googlecreativelab/anypixel/frontend/examples/ballpit/README.md

# Anypixel Ball-pit

A 2d ball pit mural for Anypixel. Press and hold an anypixel button to create a ball and grow it larger and larger; drag across buttons to create many, or mash buttons simultaneously to grow them and pit them against each other. Create balls and use them to destroy the hanging Google logo.

**Code:** Kyle Phillips

## Install:

```
npm install
```

## Build:

```
npm run build
```

## Develop:

```
npm run watch
```
