googlecreativelab/anypixel/frontend/examples/squishy/README.md

# anypixel-app-squishy

Built using Box2d and Liquidfun. This project uses a liquid simulation to create gelatinous 'squishy' letters that can be thrown around the board. 

```bash
$ npm install
$ npm run start
```

or to use watch

```bash
$ npm run watch
```
