googlecreativelab/anypixel/frontend/examples/subway/README.md

# Anypixel-Subway

MTA Subway map inspired design. Press a button to reroute the train. Built with the Anypixel Framework. 

To build it:
```sh
npm install
```
or 
```sh
npm run build
```

To run it, you'll need to install [Anypixel-Previewer](https://github.com/googlecreativelab/anypixel-previewer) first. Then in the app's root directory, do:
```sh   
preview
```
