googlecreativelab/anypixel/frontend/examples/blocksquish/preview.jpg

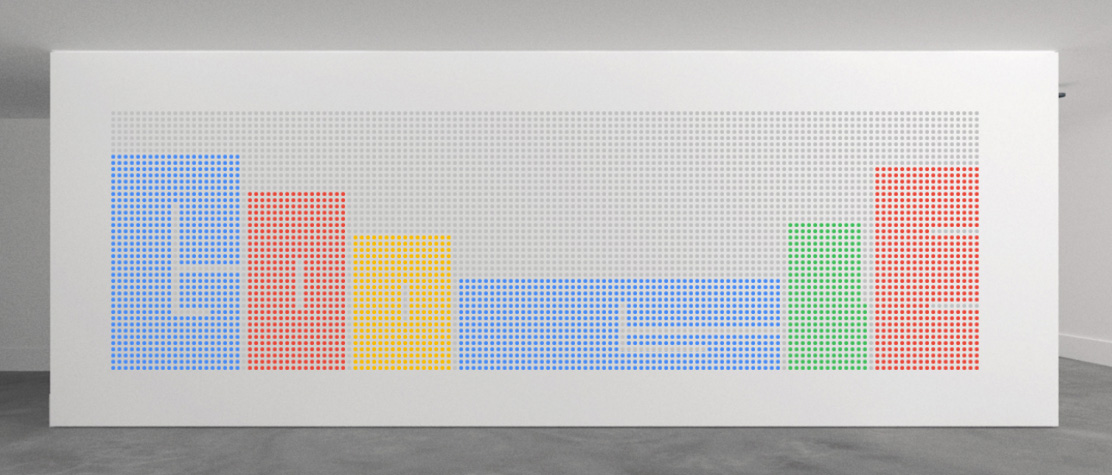
frontend/examples/blocksquish/preview.jpg
