googlecreativelab/anypixel/frontend/examples/heatmap/preview.jpg

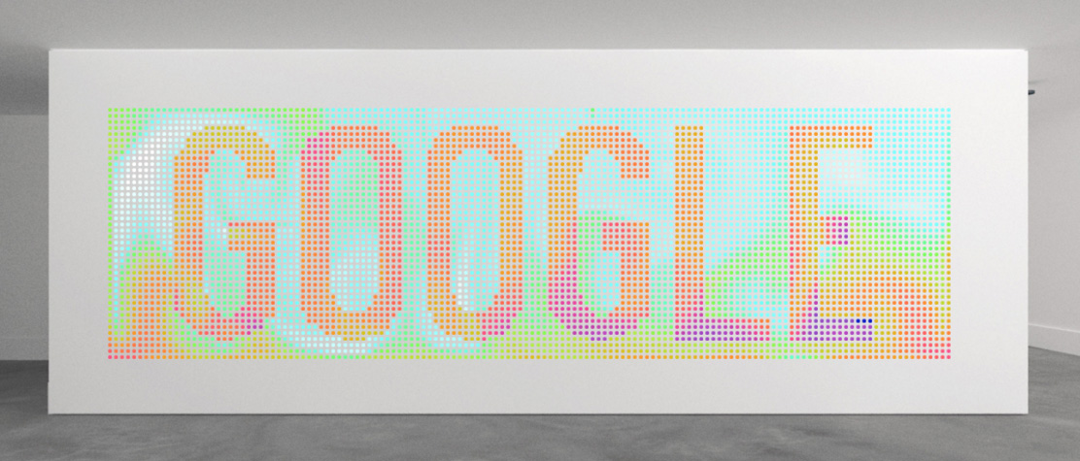
frontend/examples/heatmap/preview.jpg
