googlecreativelab/anypixel/frontend/examples/hyperspace/preview.jpg

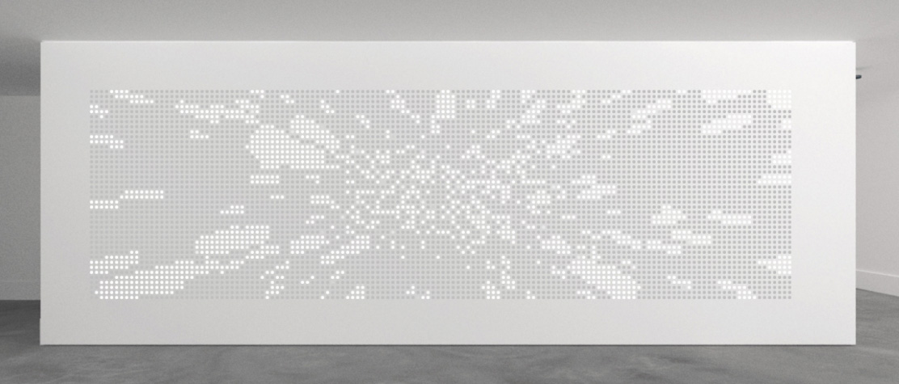
frontend/examples/hyperspace/preview.jpg
