googlecreativelab/anypixel/frontend/examples/reaction/preview.jpg

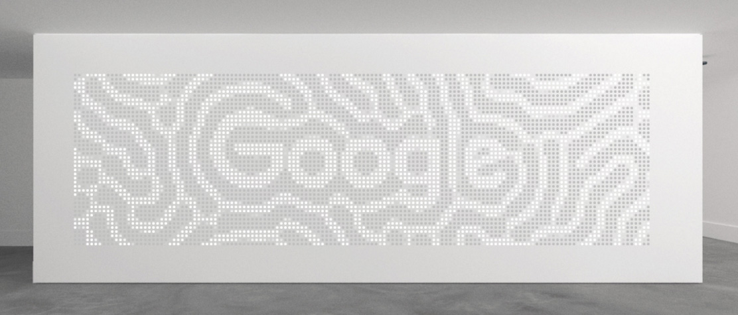
frontend/examples/reaction/preview.jpg
