googlecreativelab/anypixel/hardware/pcb/controller/controller-r3-bottom.pdf

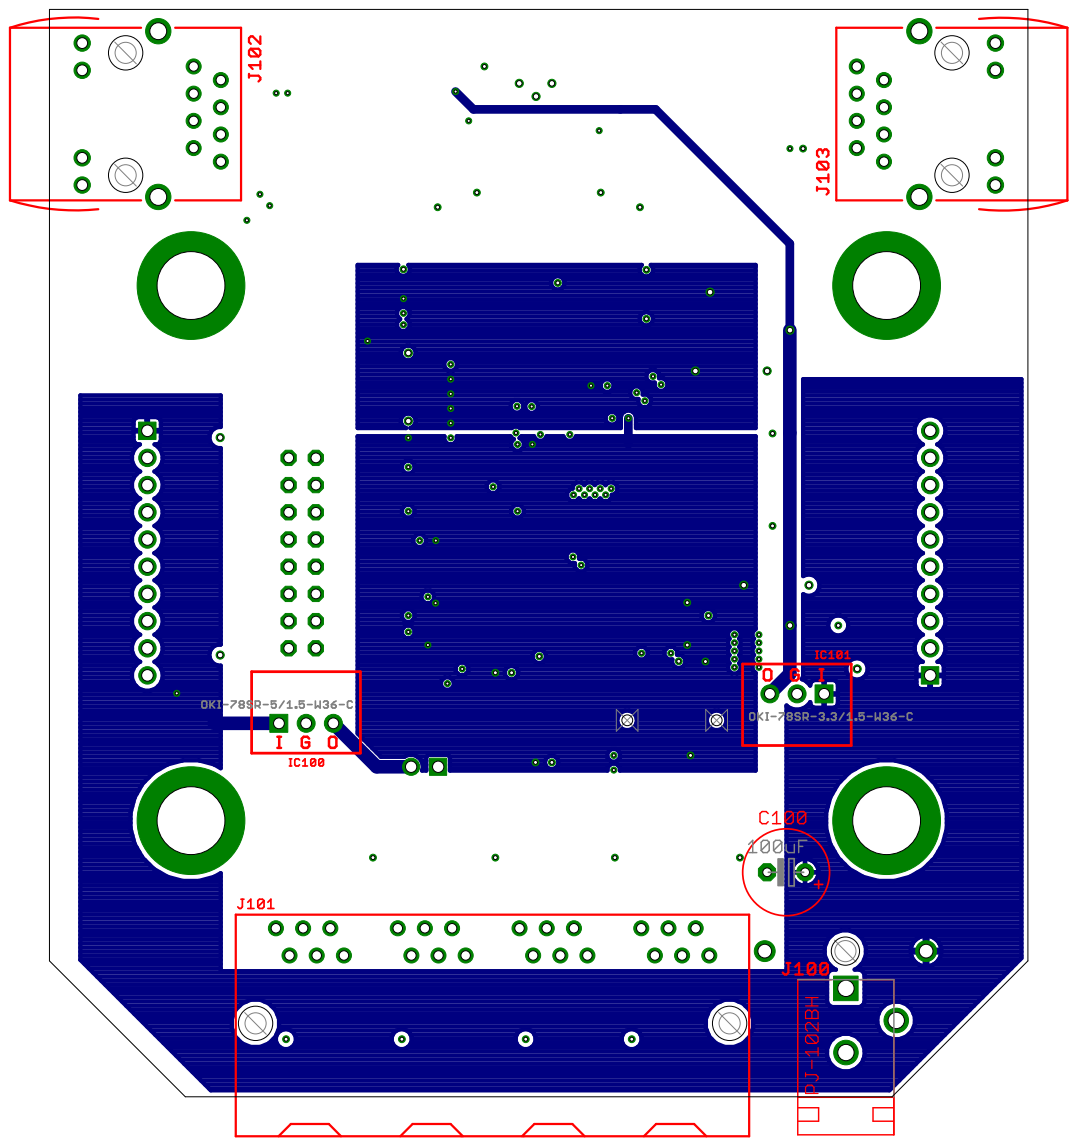
[picture p40: page 1]
