googlecreativelab/anypixel/hardware/pcb/controller/controller-r3-schematics.pdf

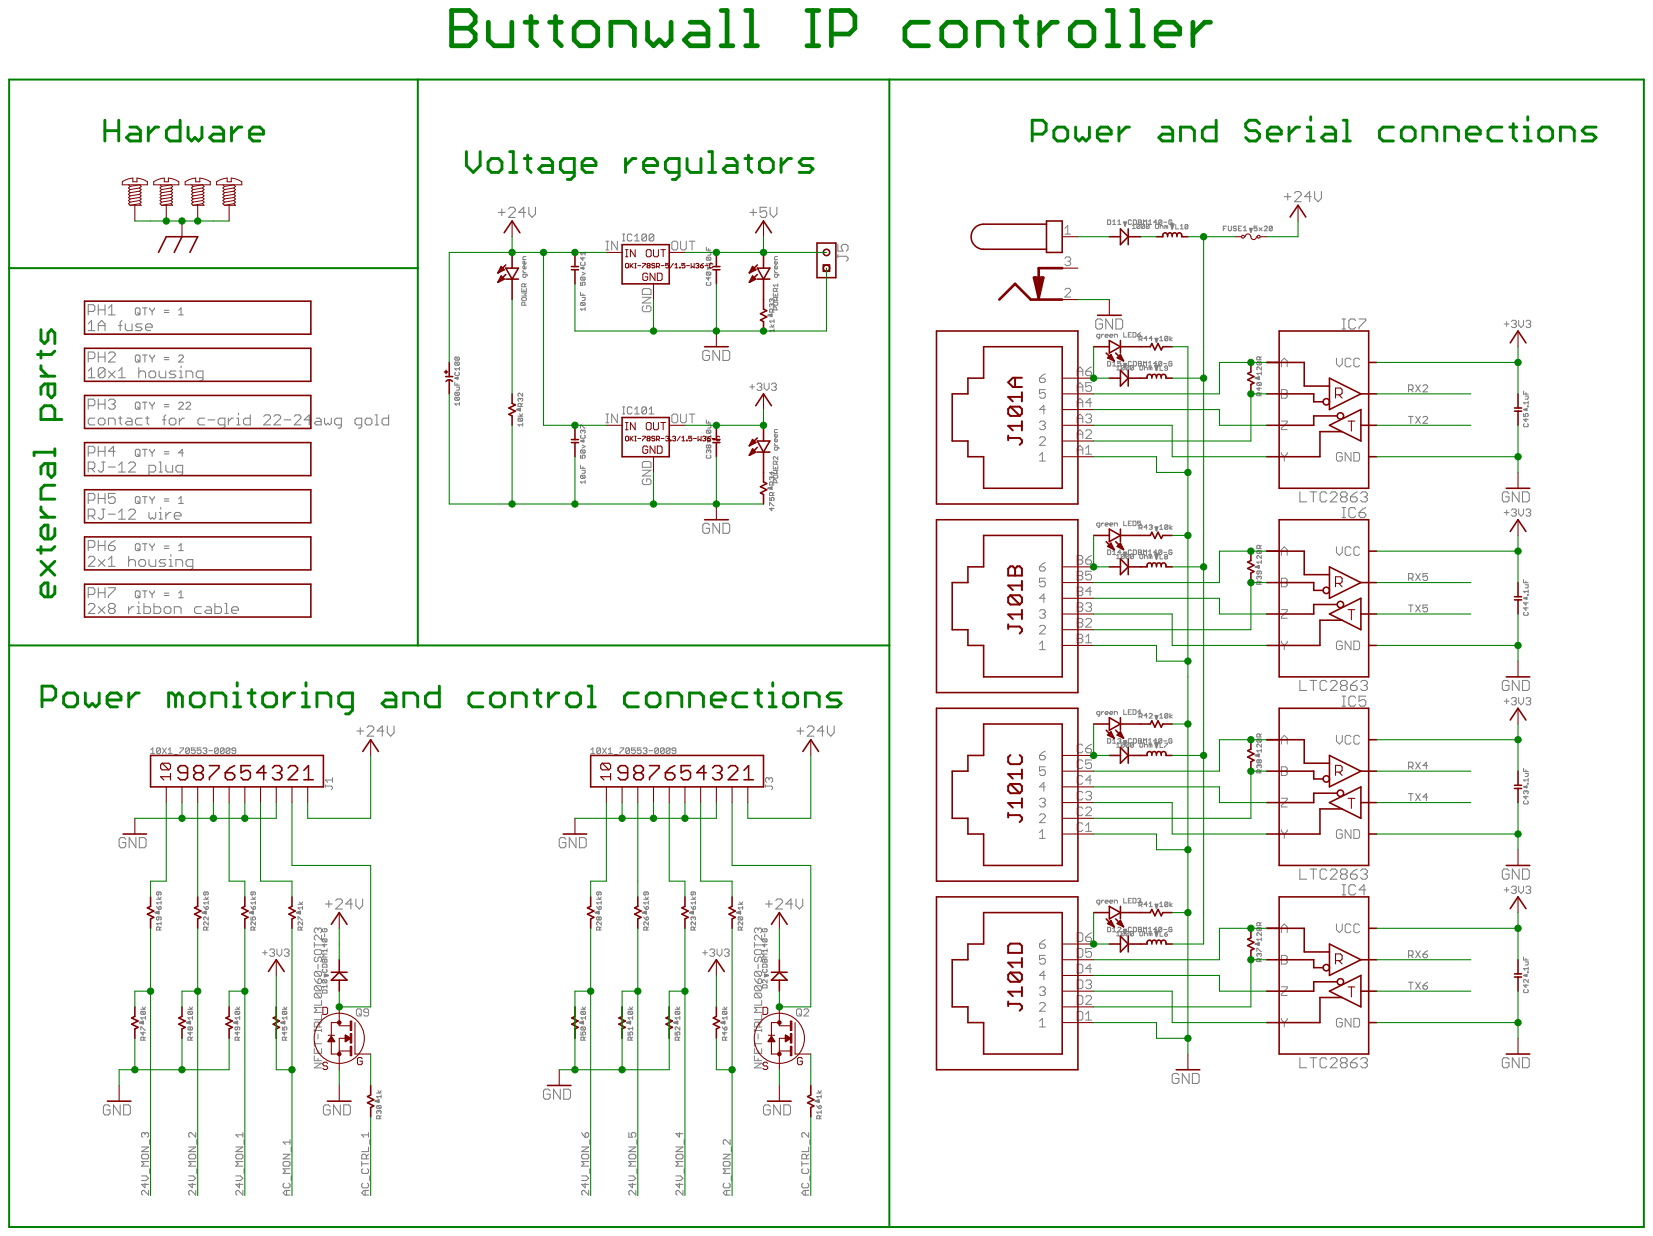
[picture p41: page 1]

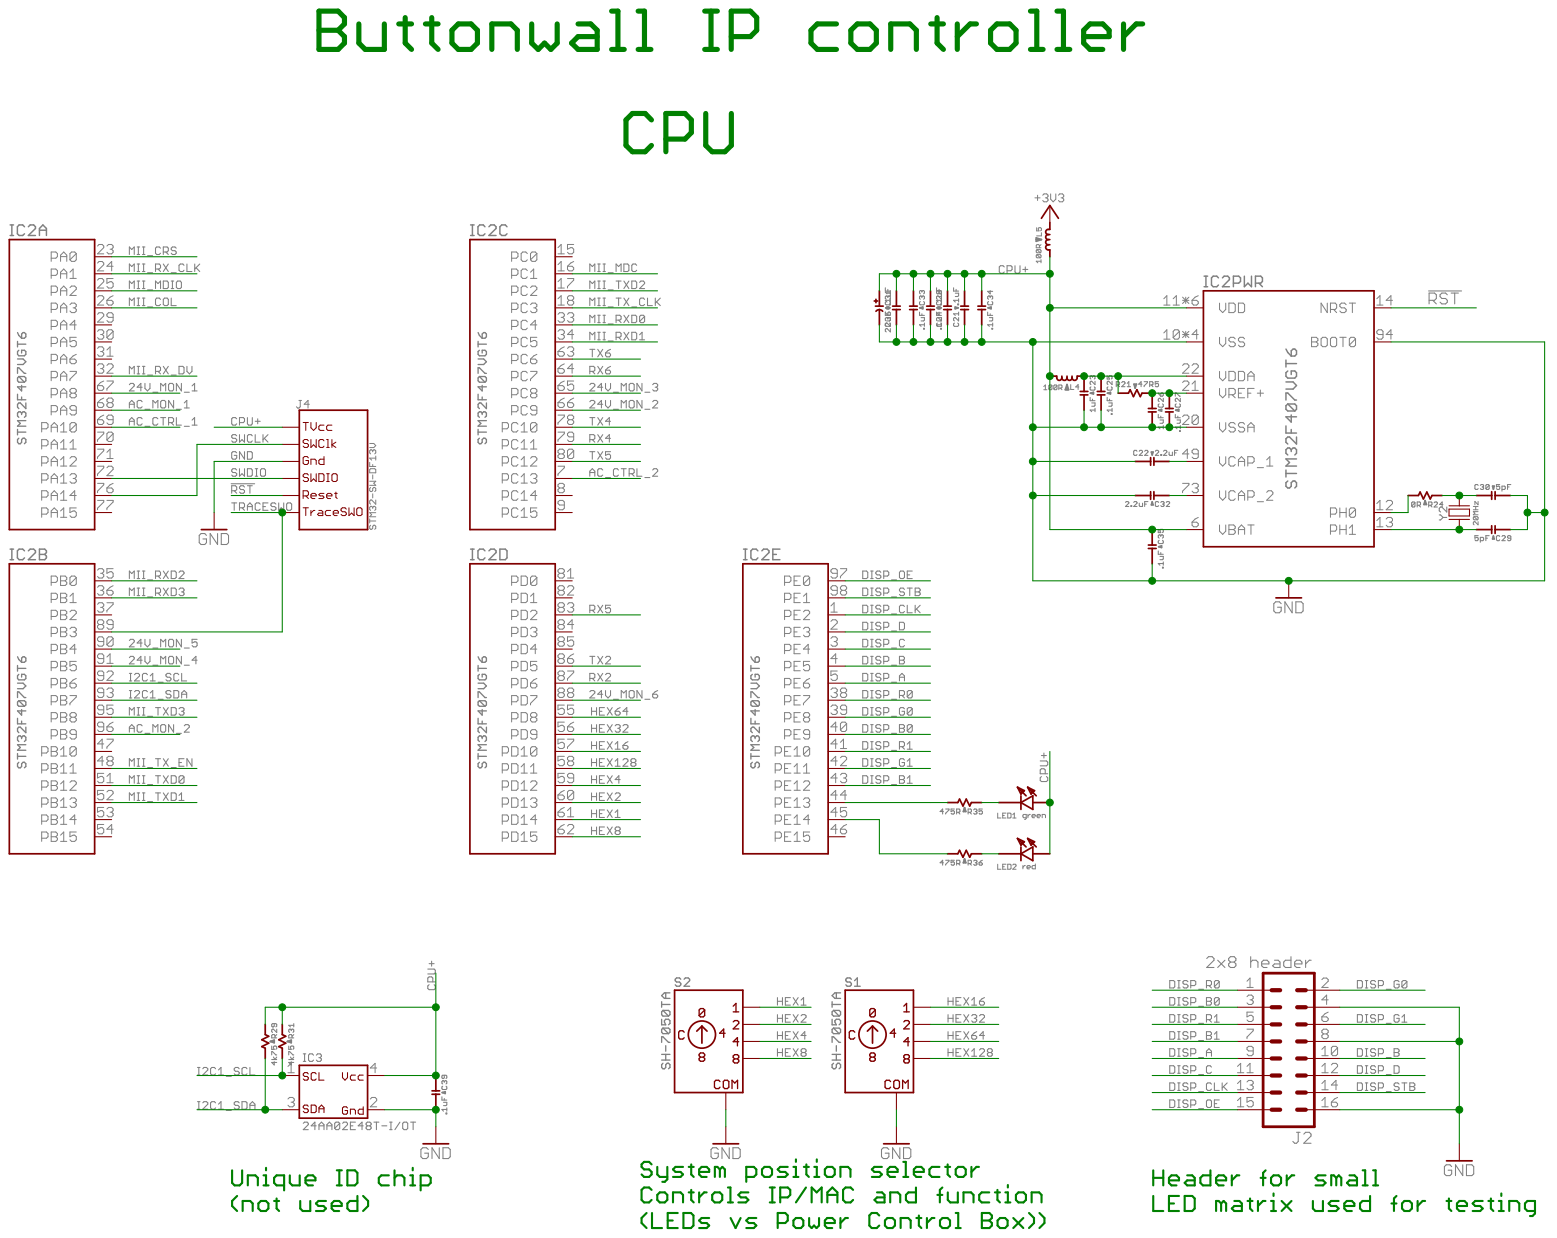
[picture p42: page 2]

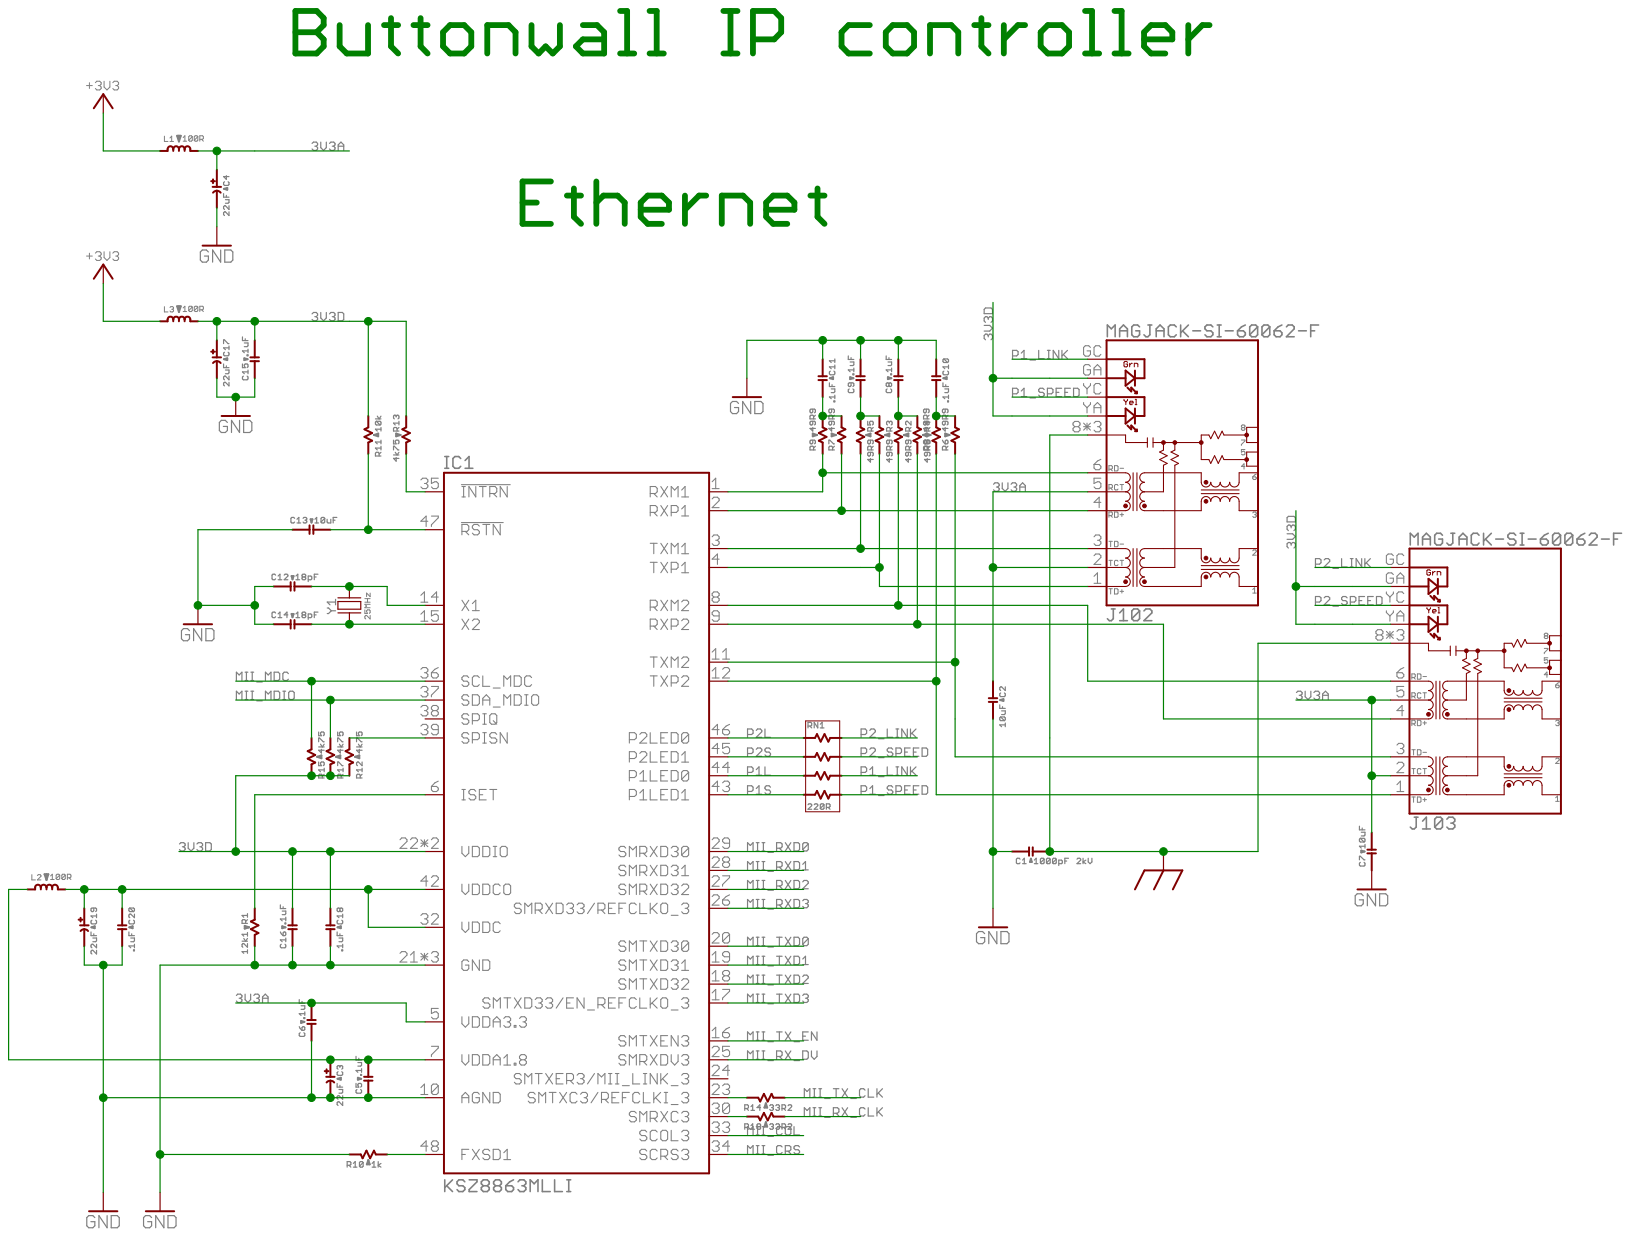
[picture p43: page 3]
