googlecreativelab/anypixel/hardware/pcb/controller/controller-r3-top.pdf

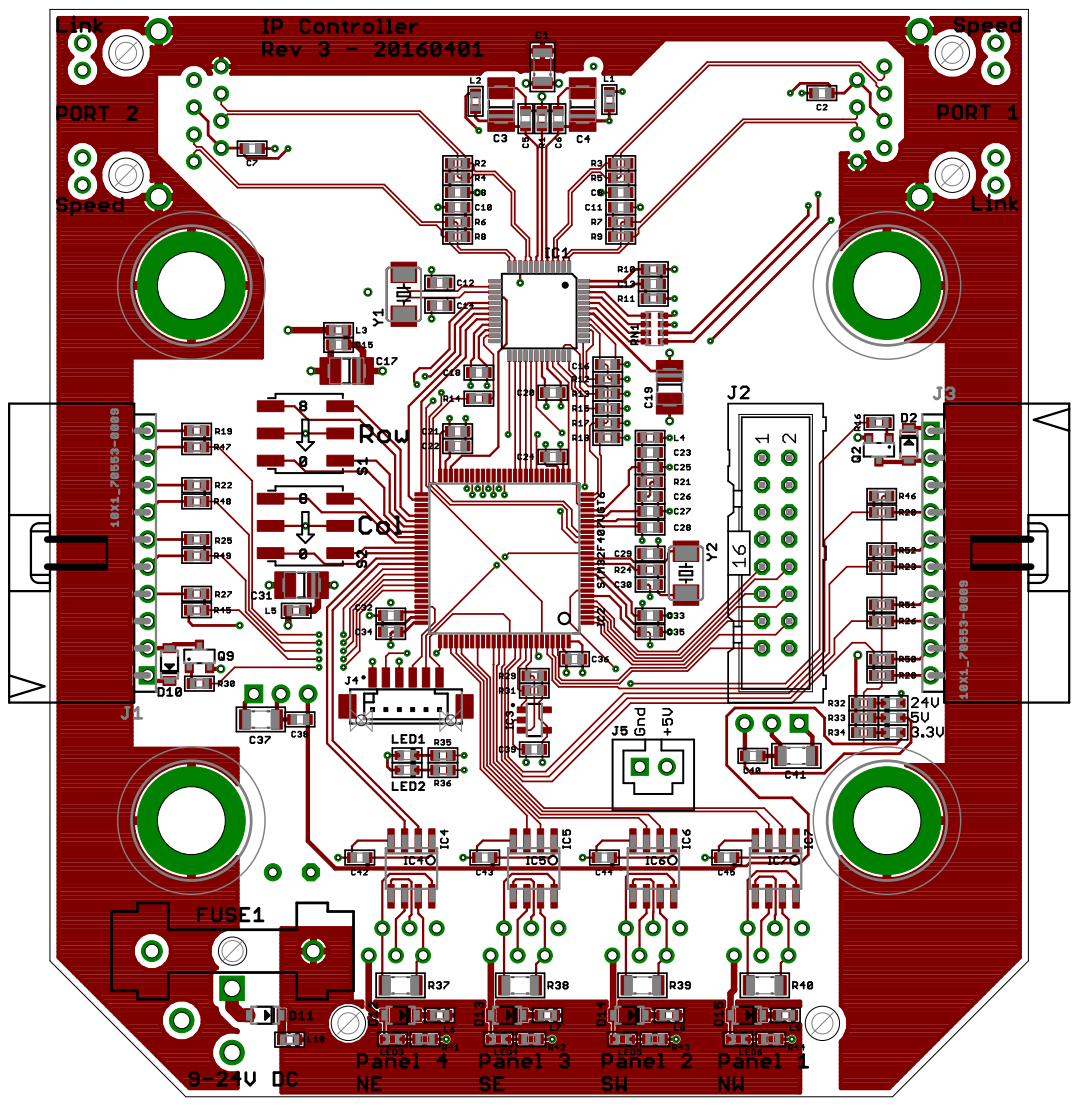
[picture p44: page 1]
