googlecreativelab/anypixel/hardware/pcb/controller/controller-r3.pdf

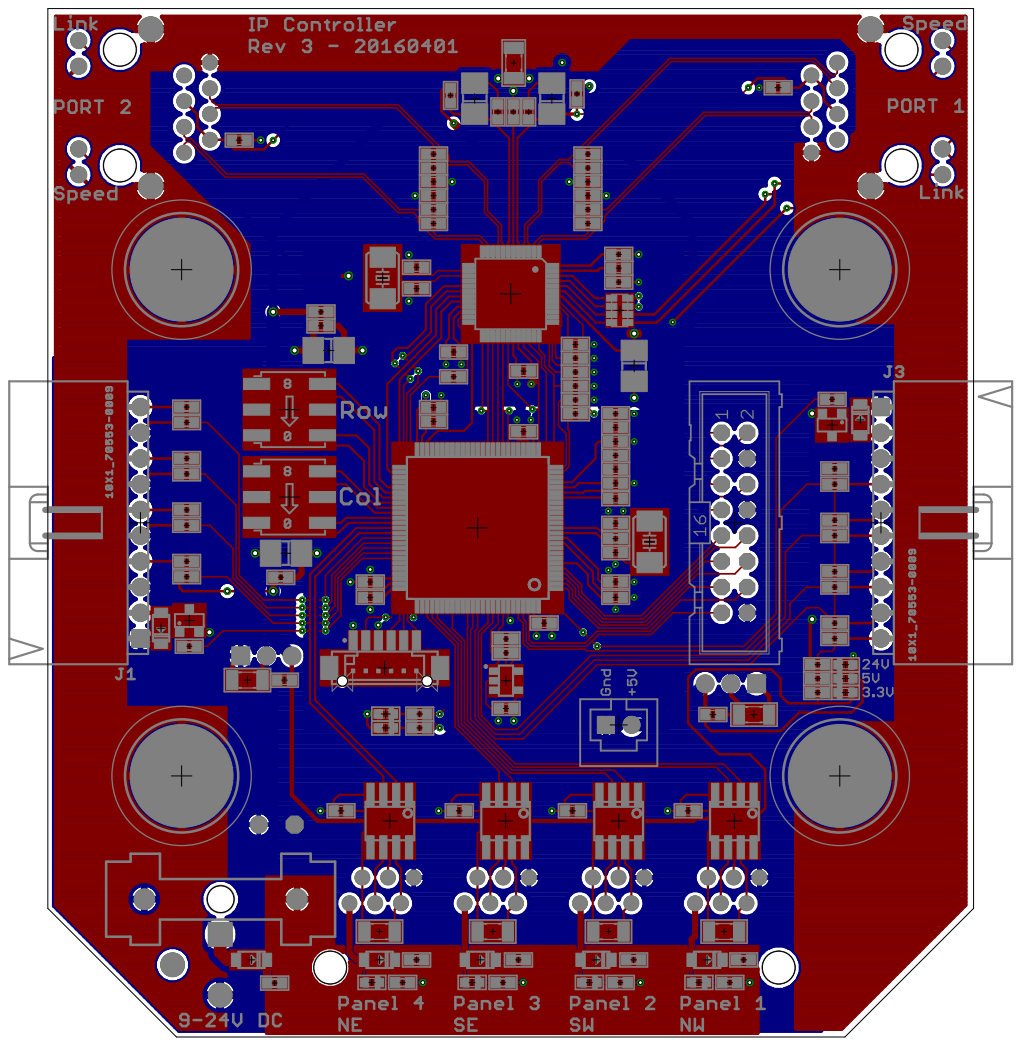
[picture p45: page 1]
