googlecreativelab/anypixel/hardware/pcb/display/display-r2-bottom.pdf

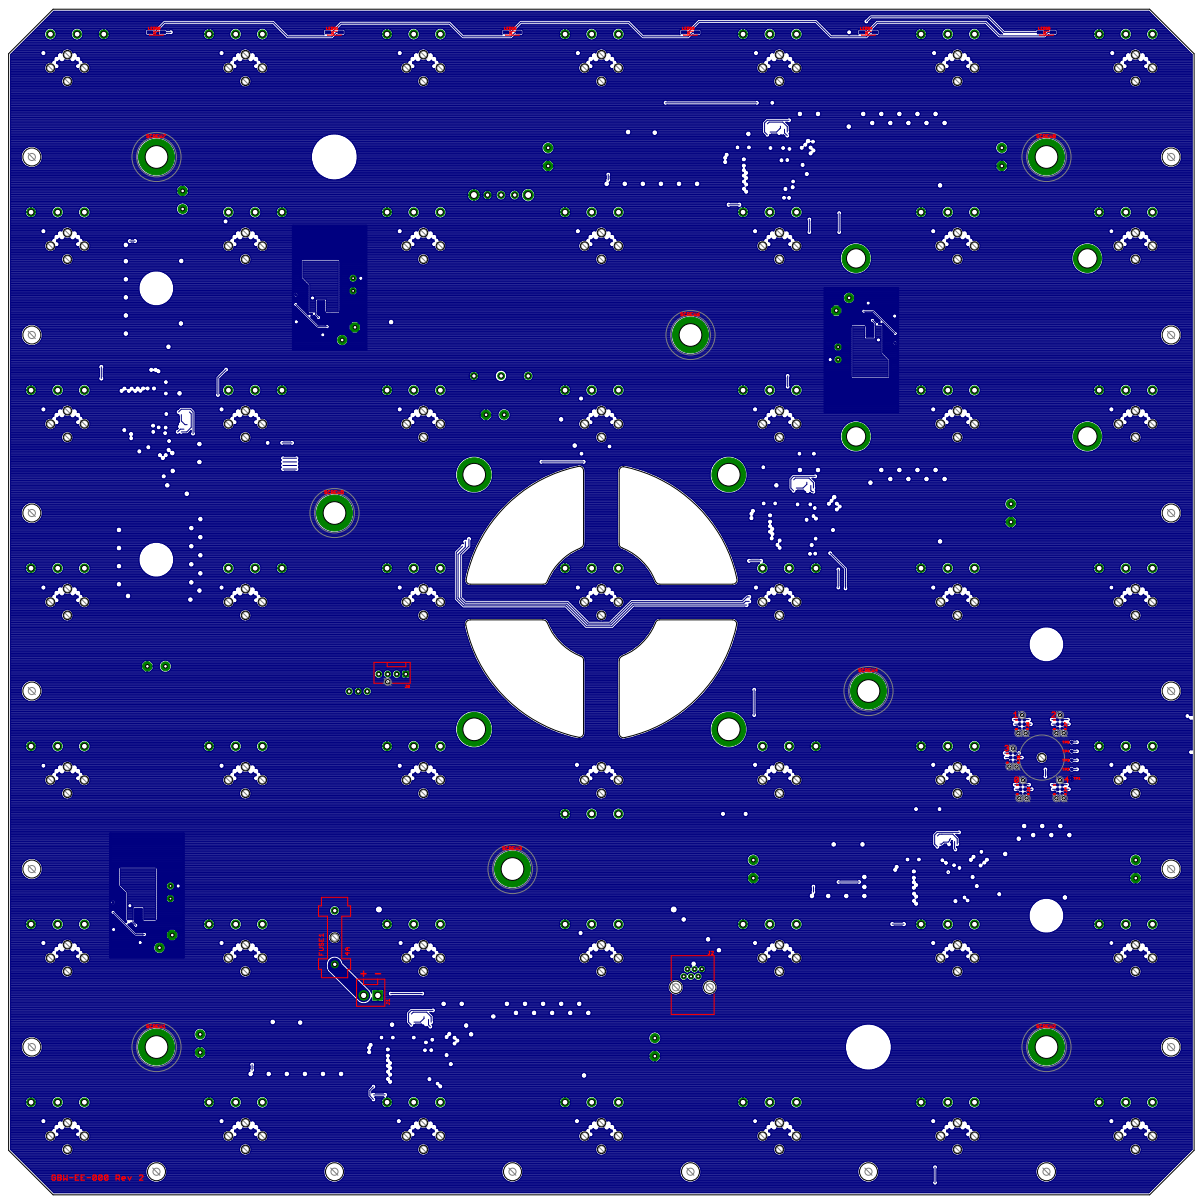
[picture p46: page 1]
