googlecreativelab/anypixel/hardware/pcb/display/display-r2-schematic.pdf

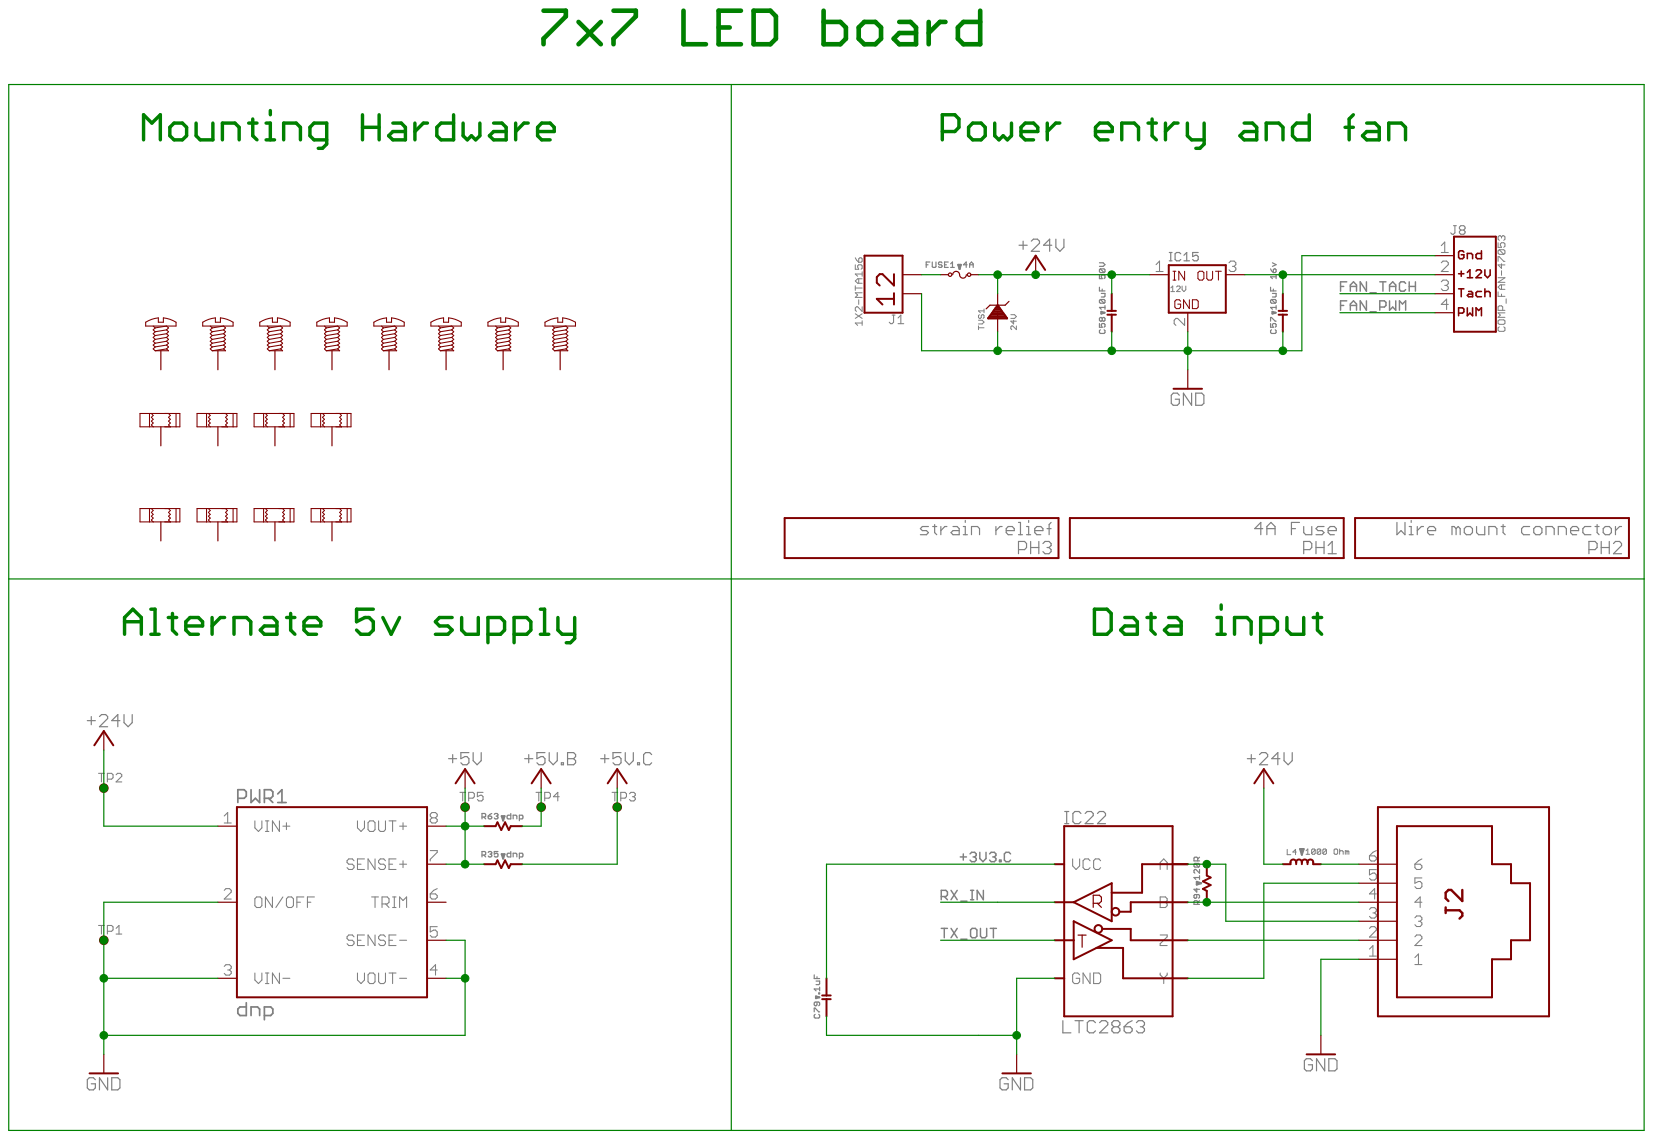
[picture p47: page 1]

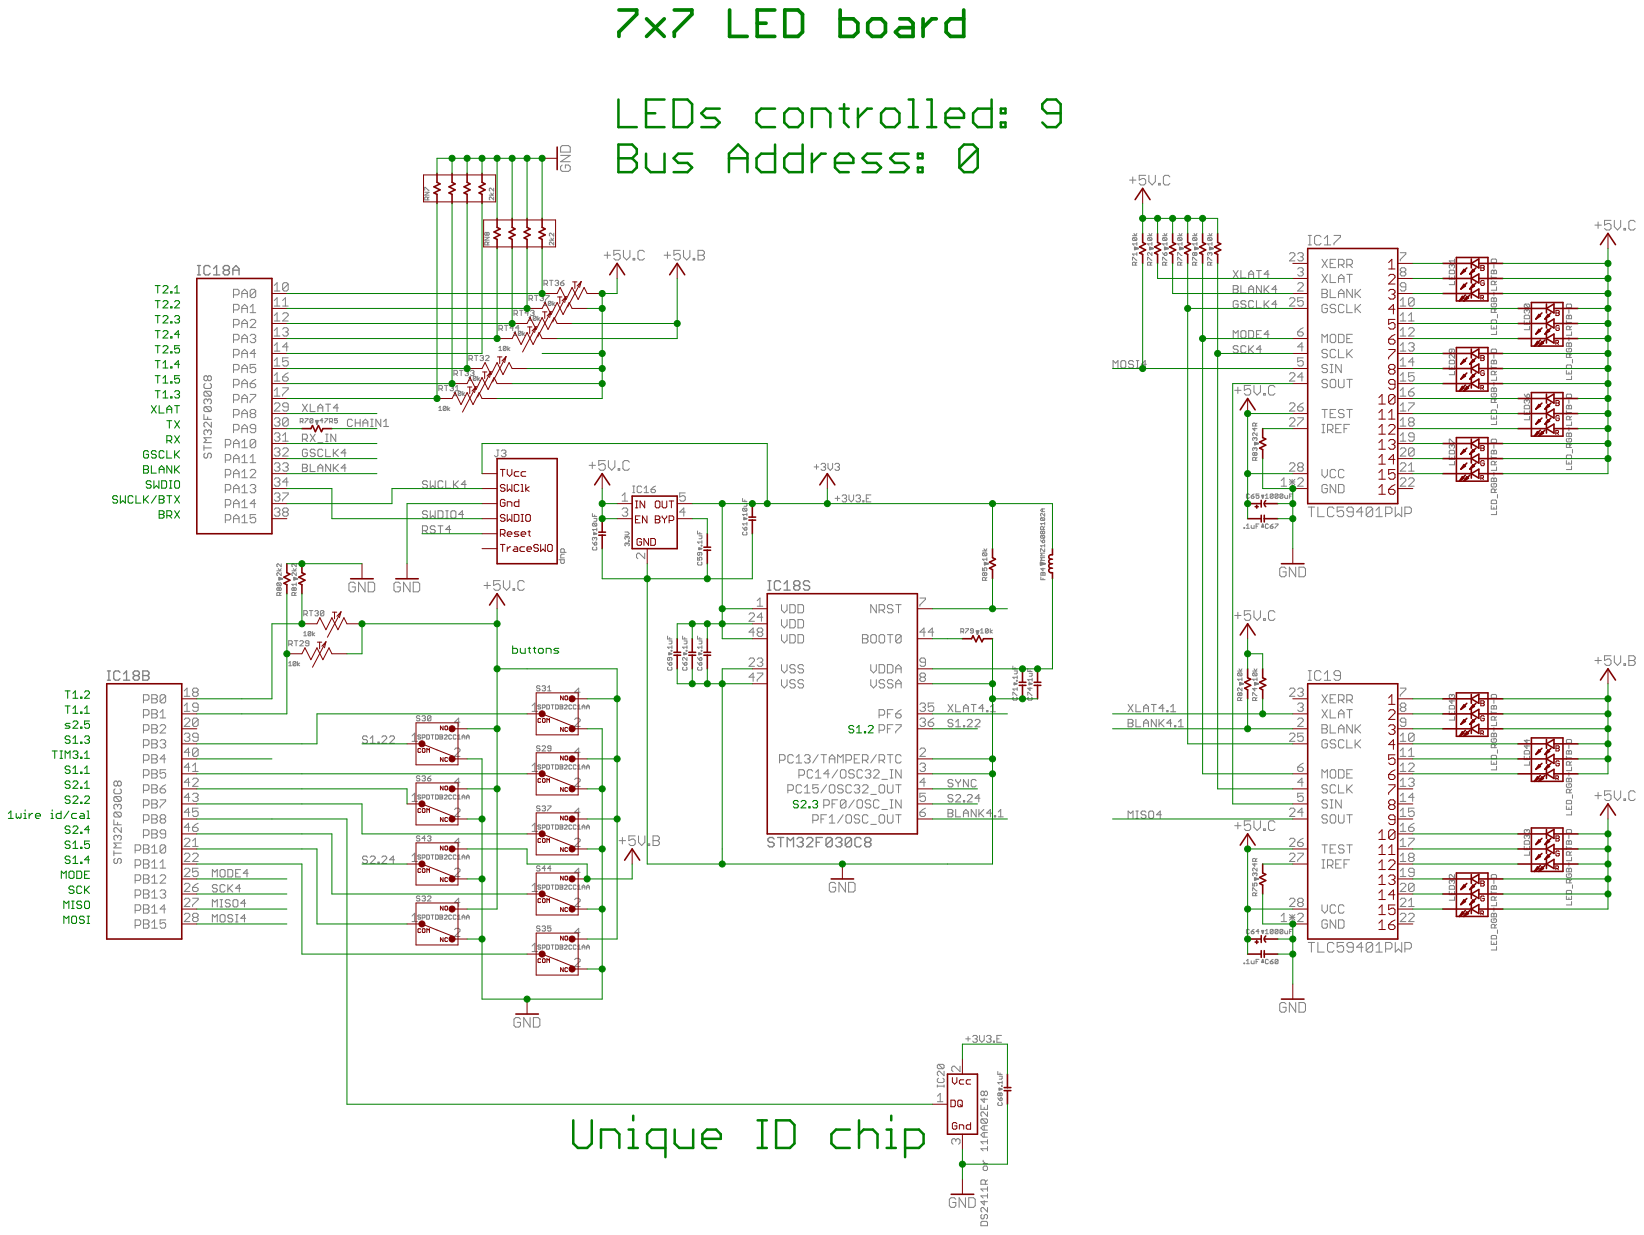
[picture p48: page 2]

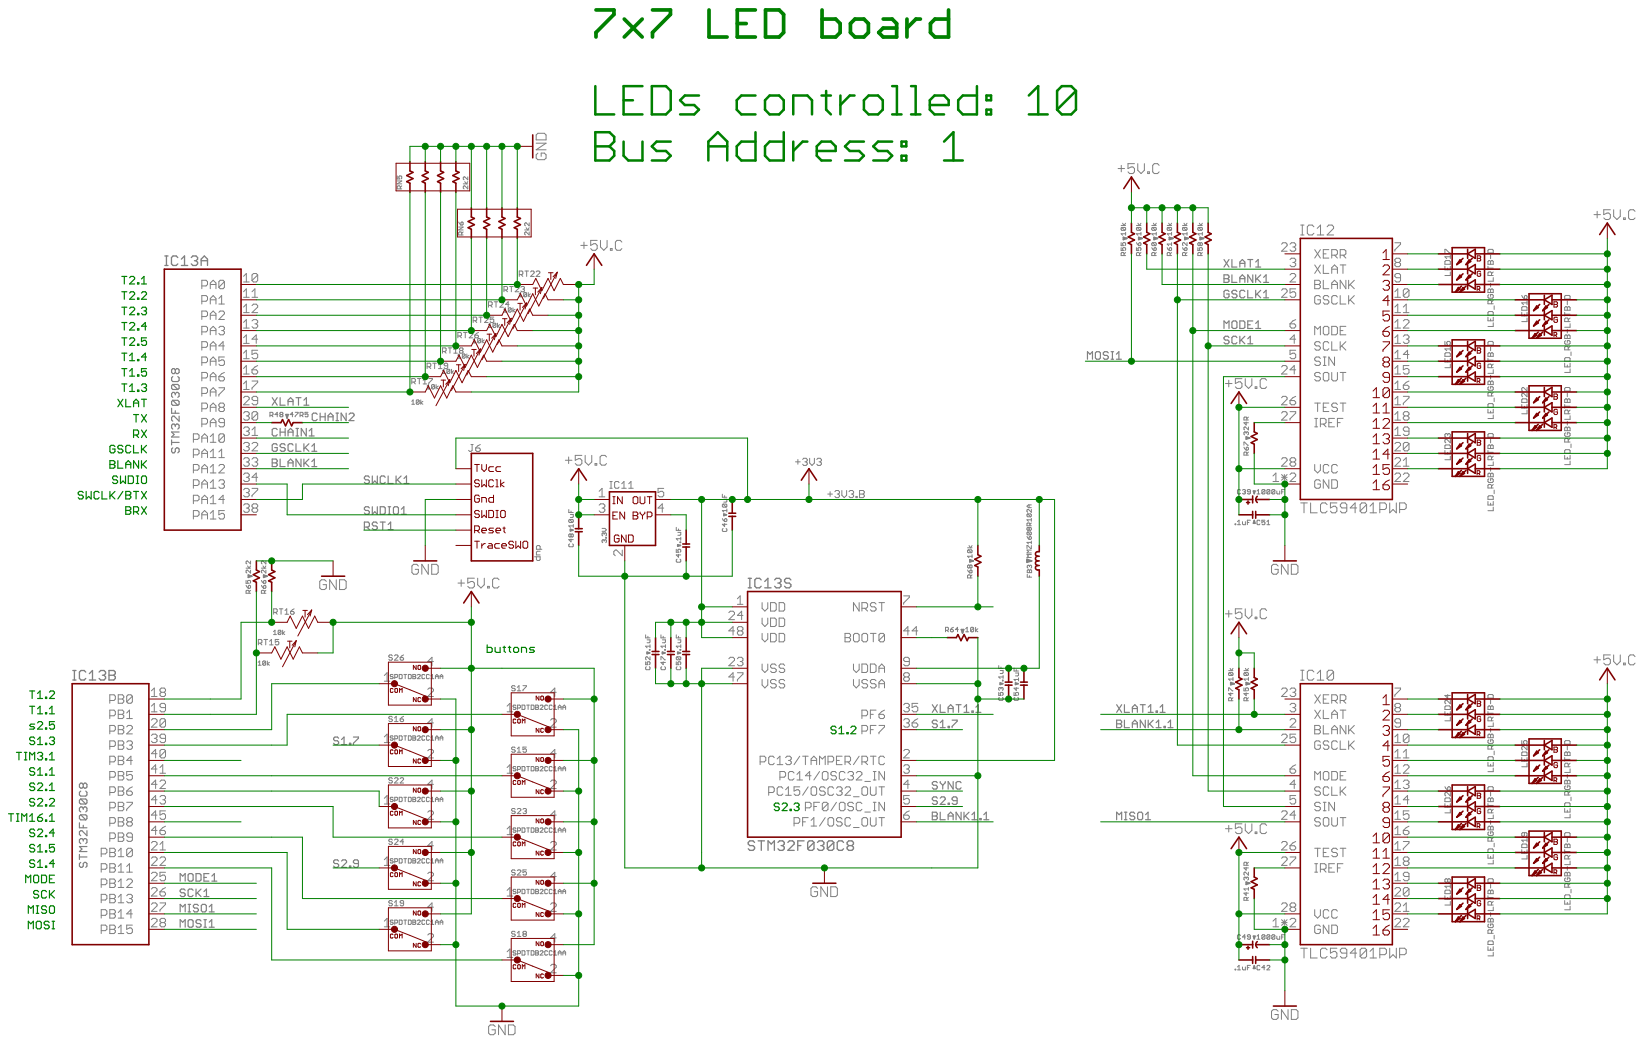
[picture p49: page 3]

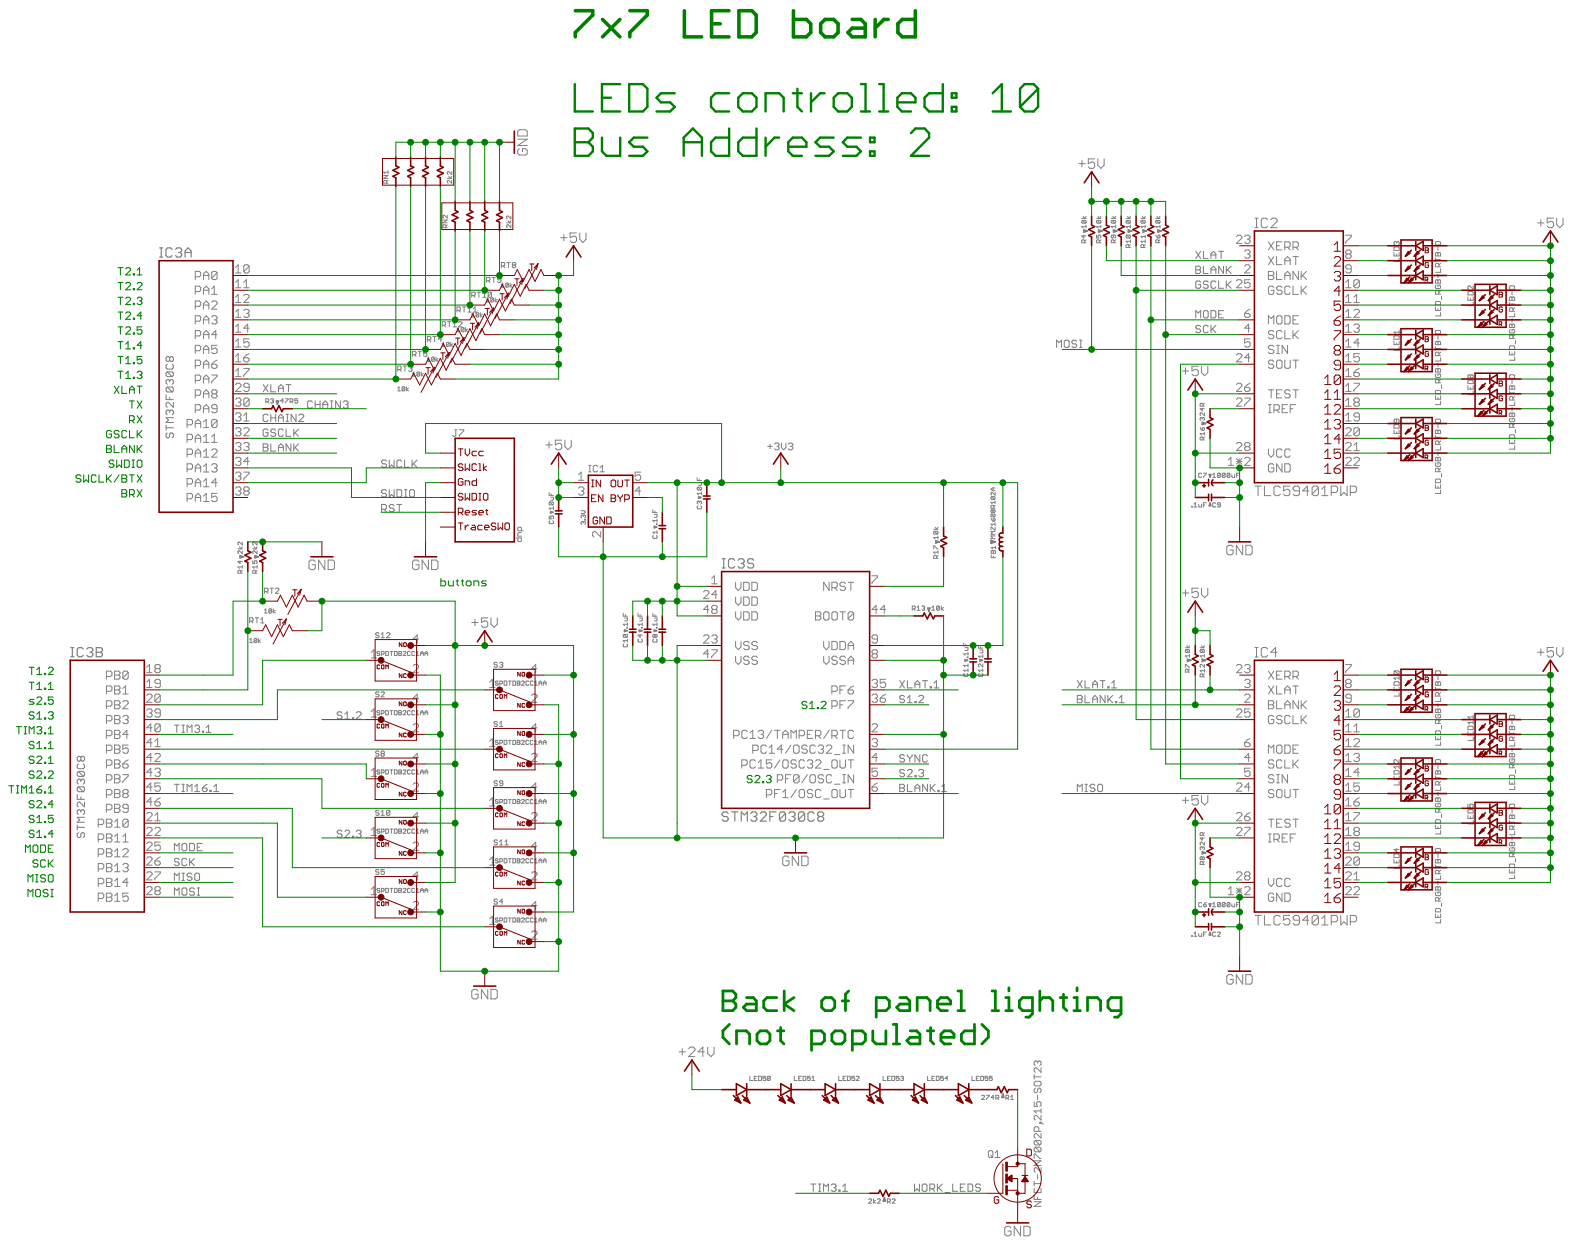
[picture p50: page 4]

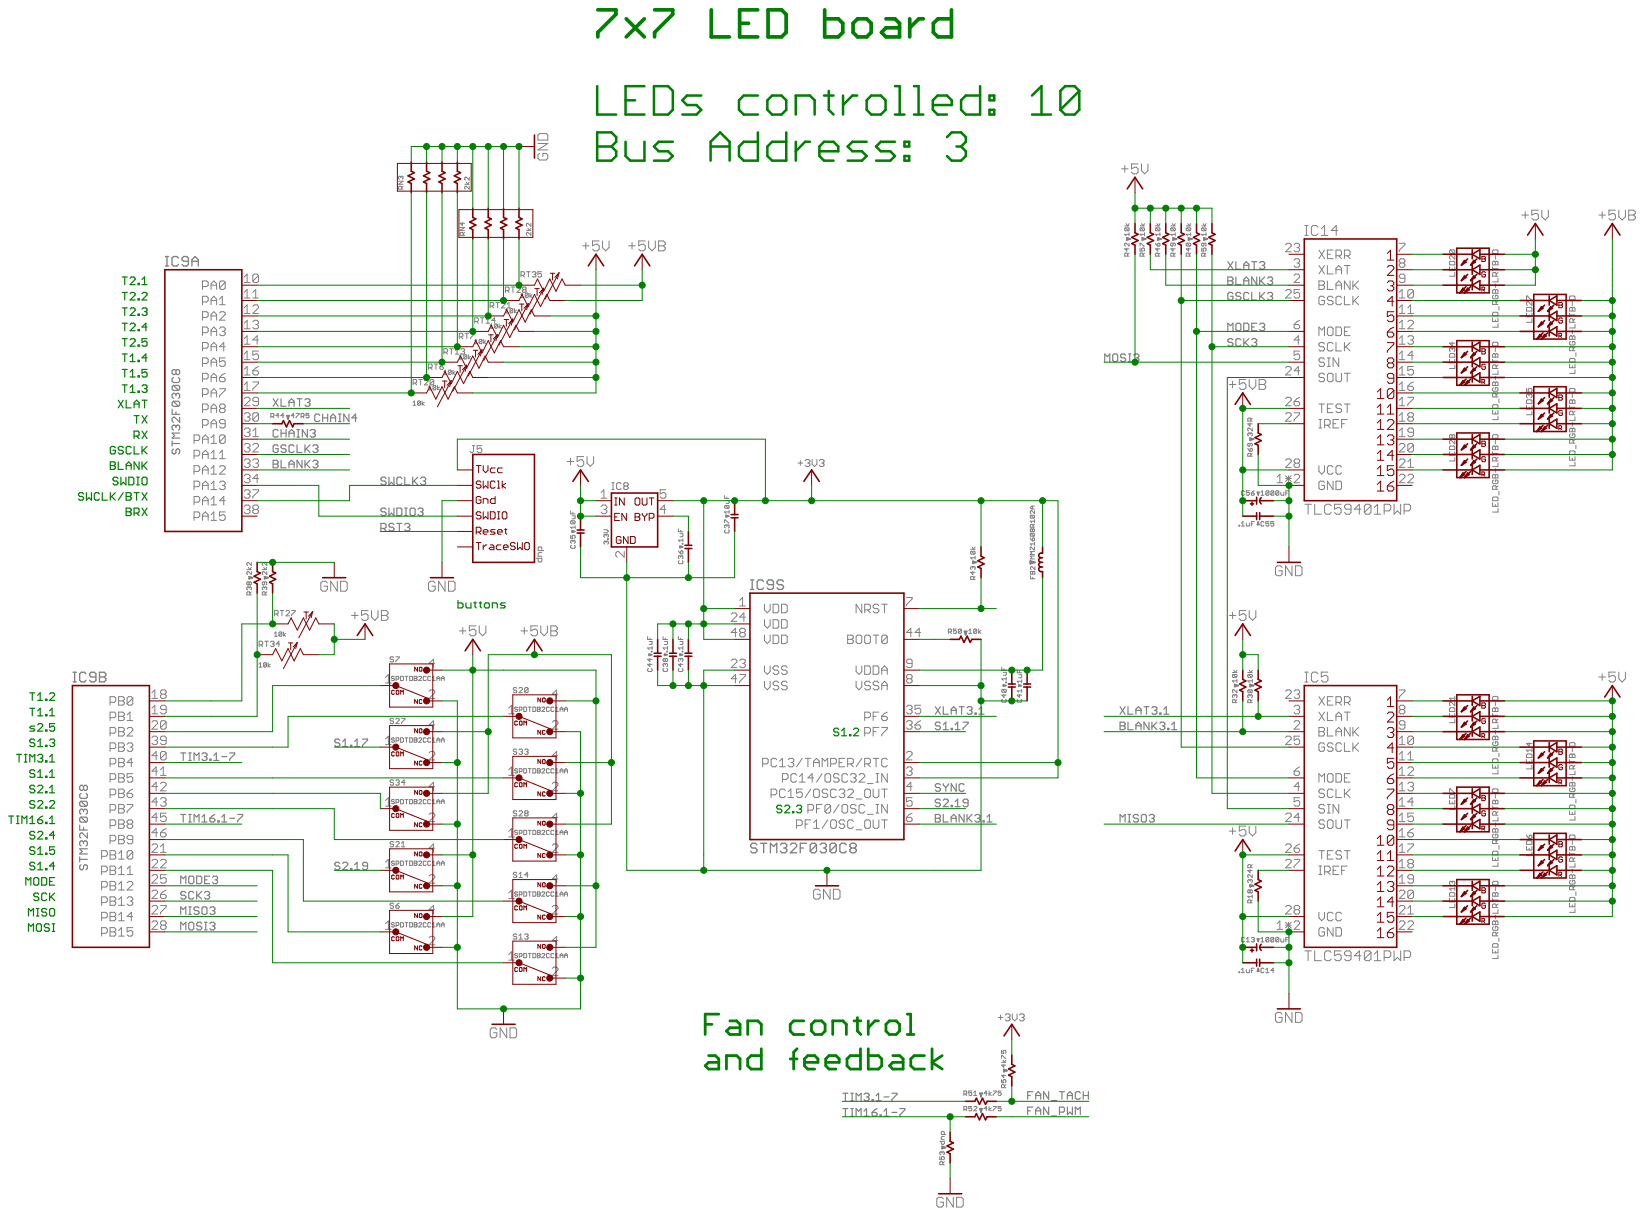
[picture p51: page 5]

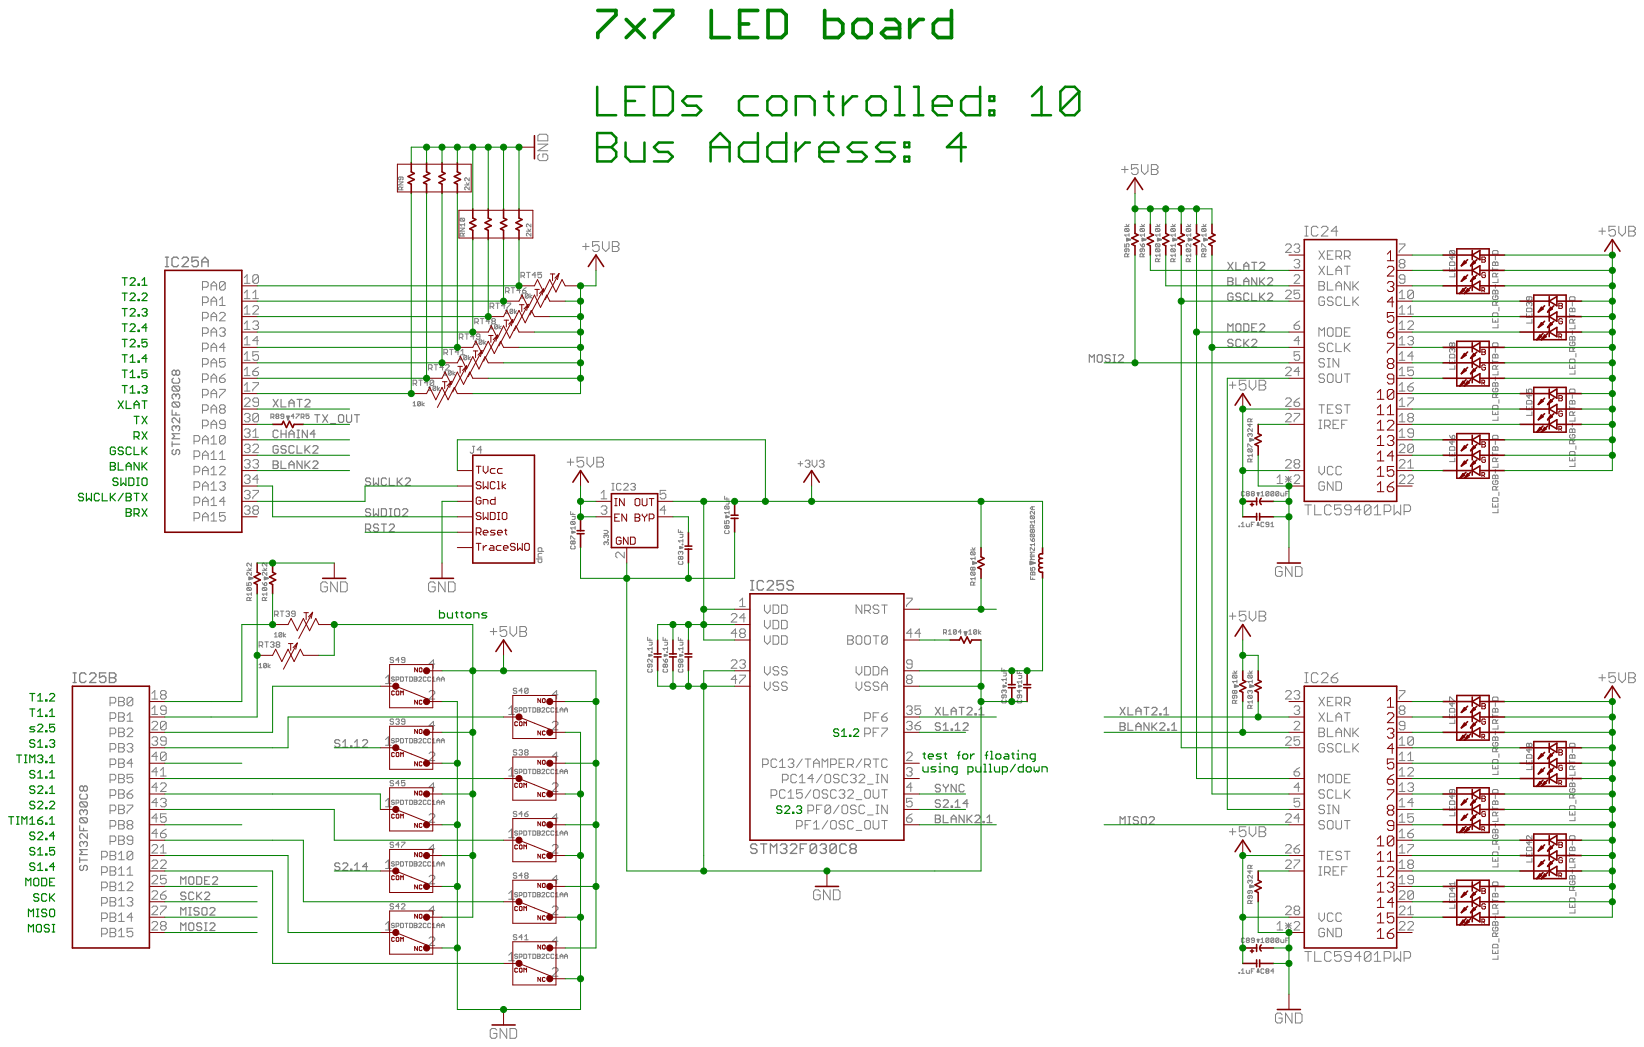
[picture p52: page 6]

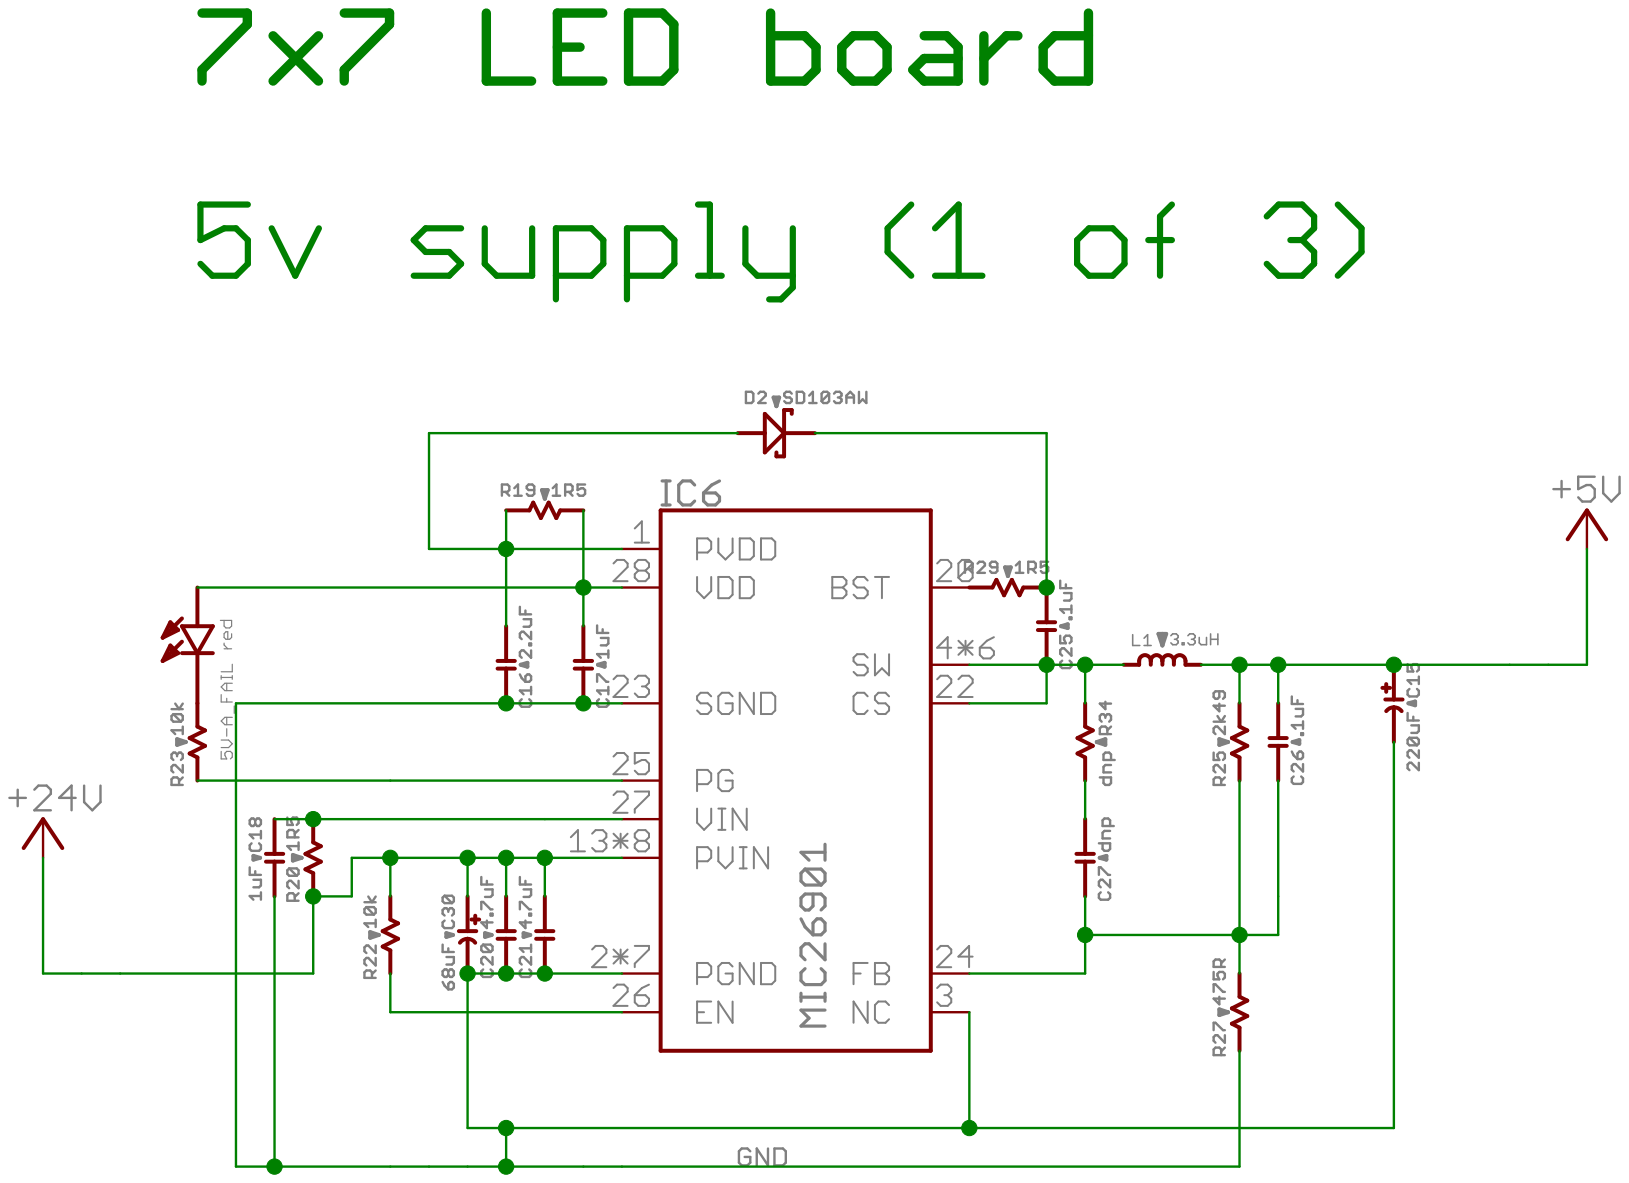
[picture p53: page 7]

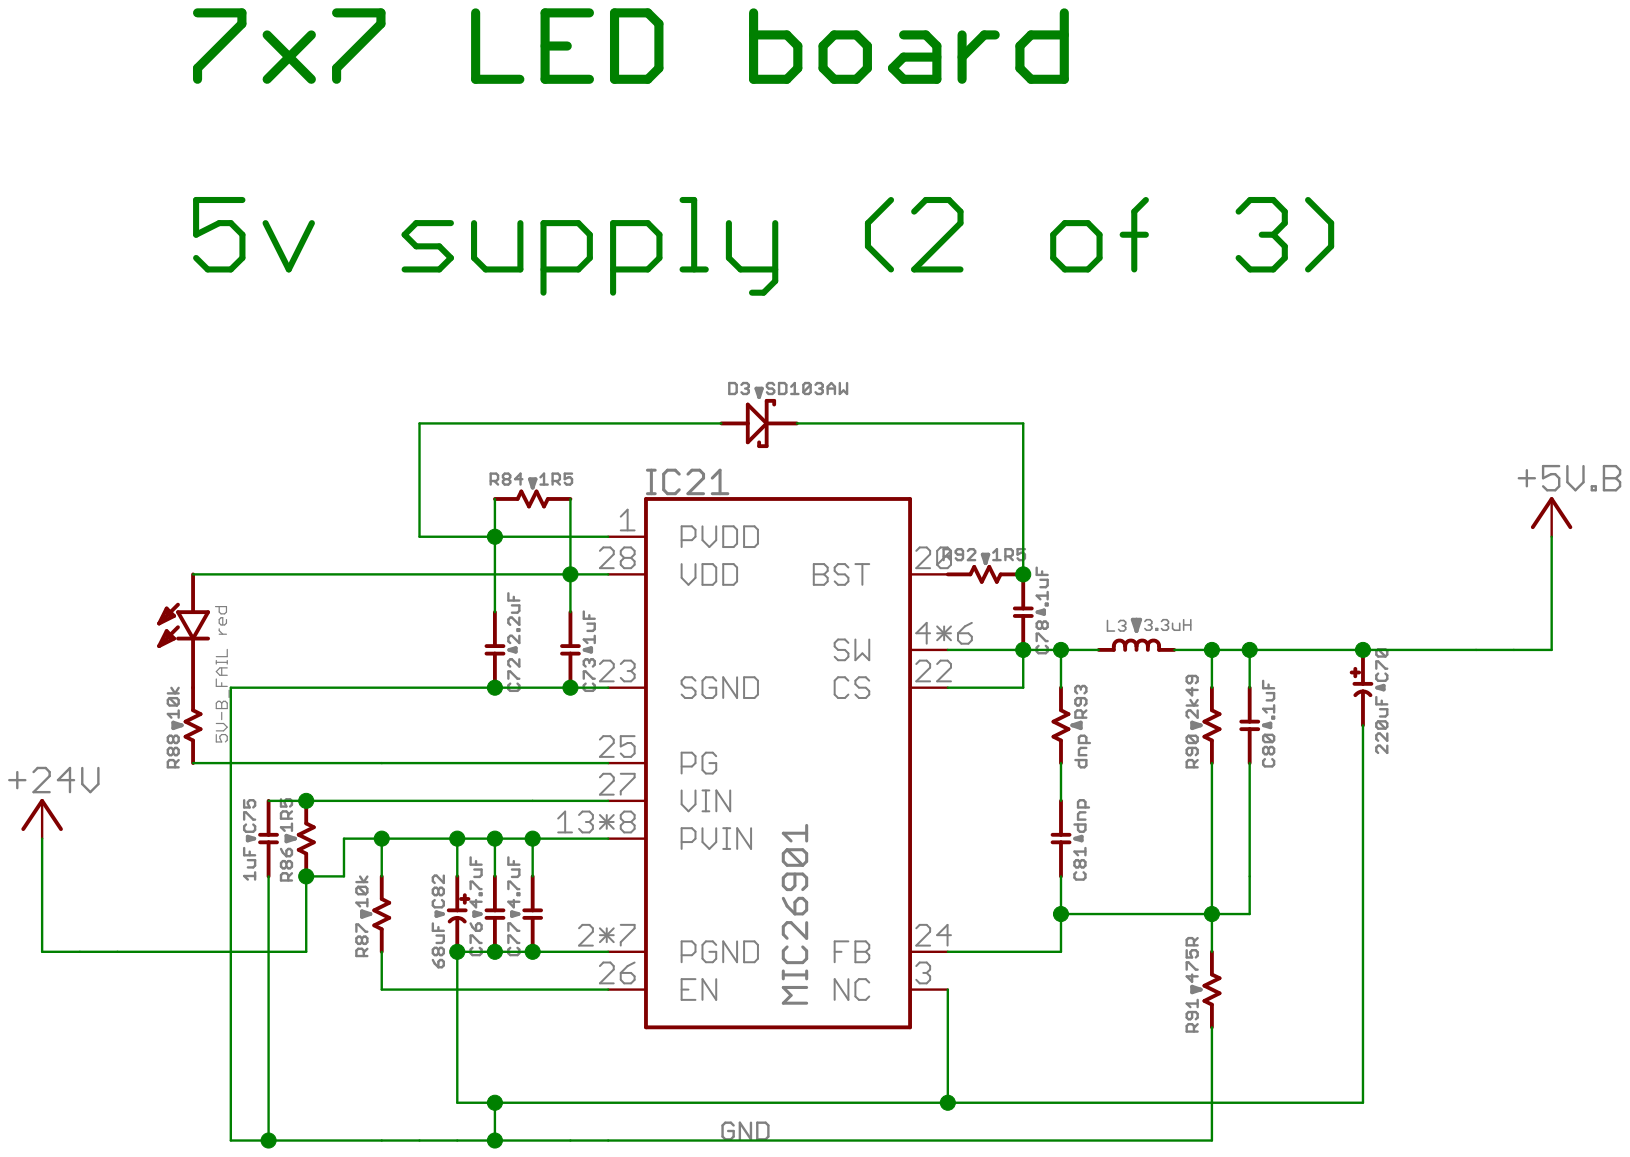
[picture p54: page 8]

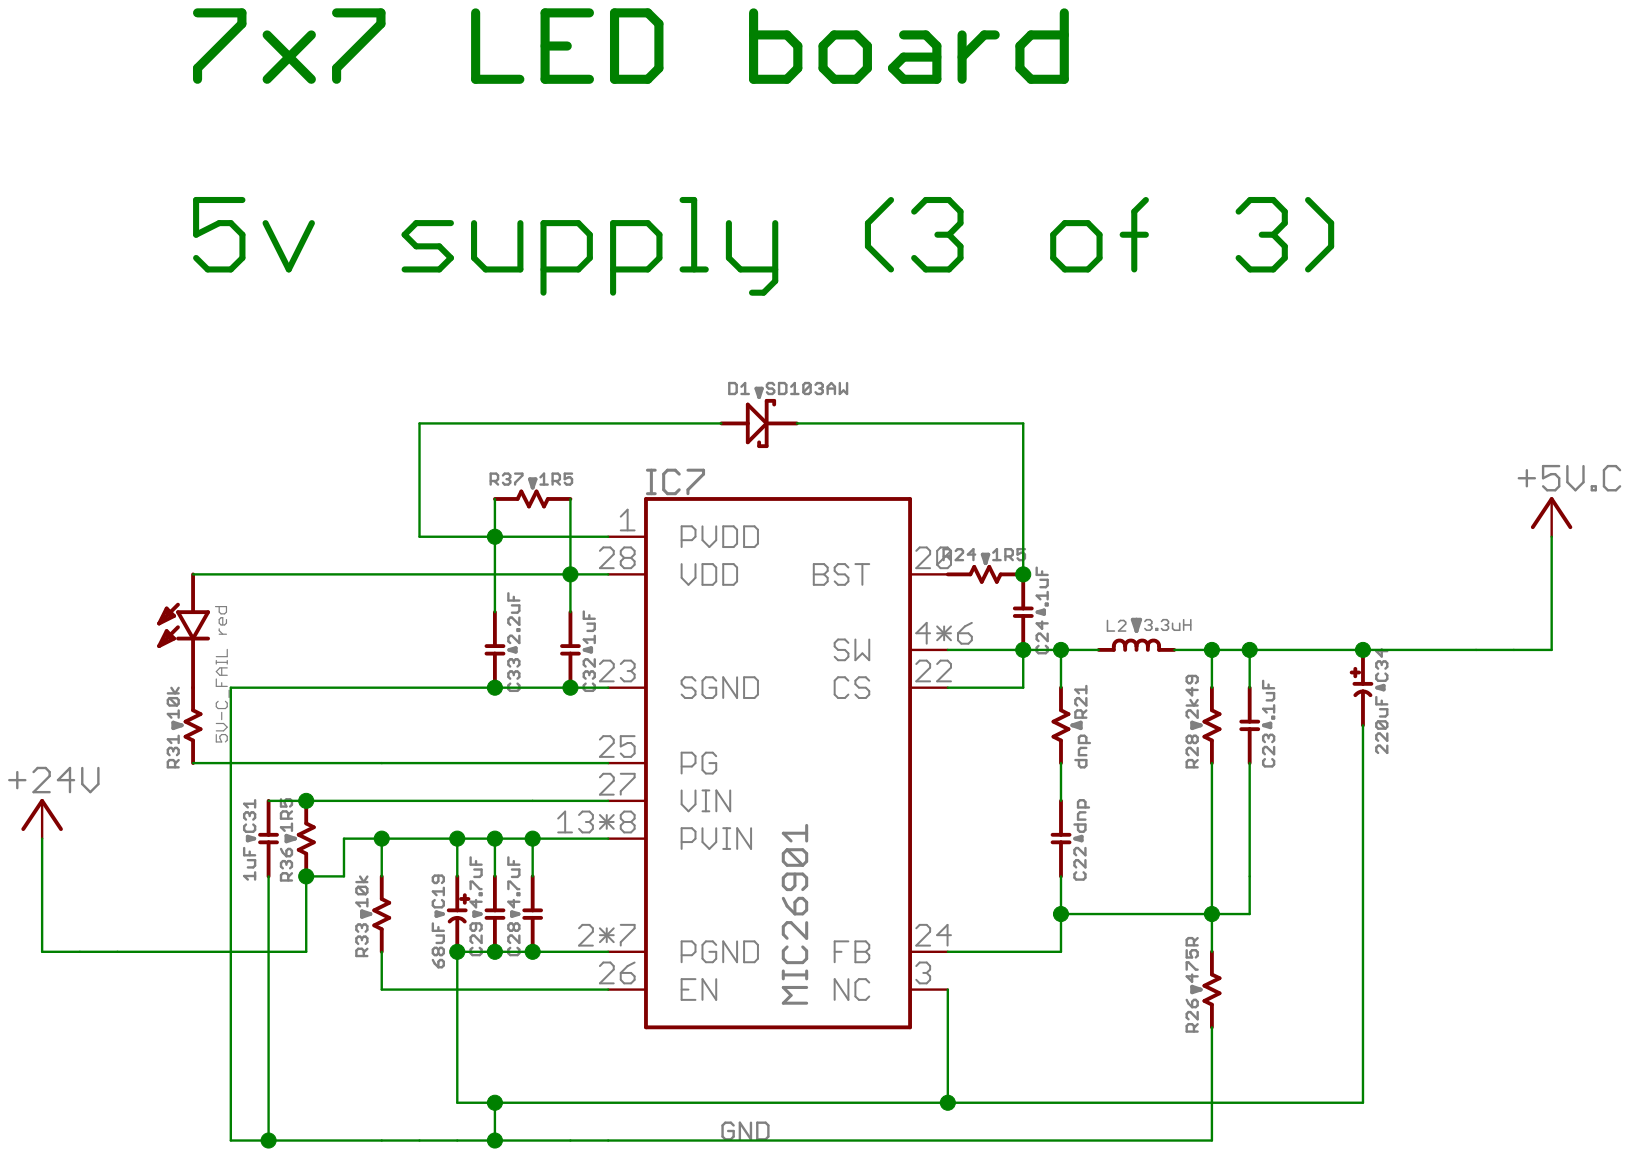
[picture p55: page 9]
