googlecreativelab/anypixel/hardware/pcb/display/display-r2-top.pdf

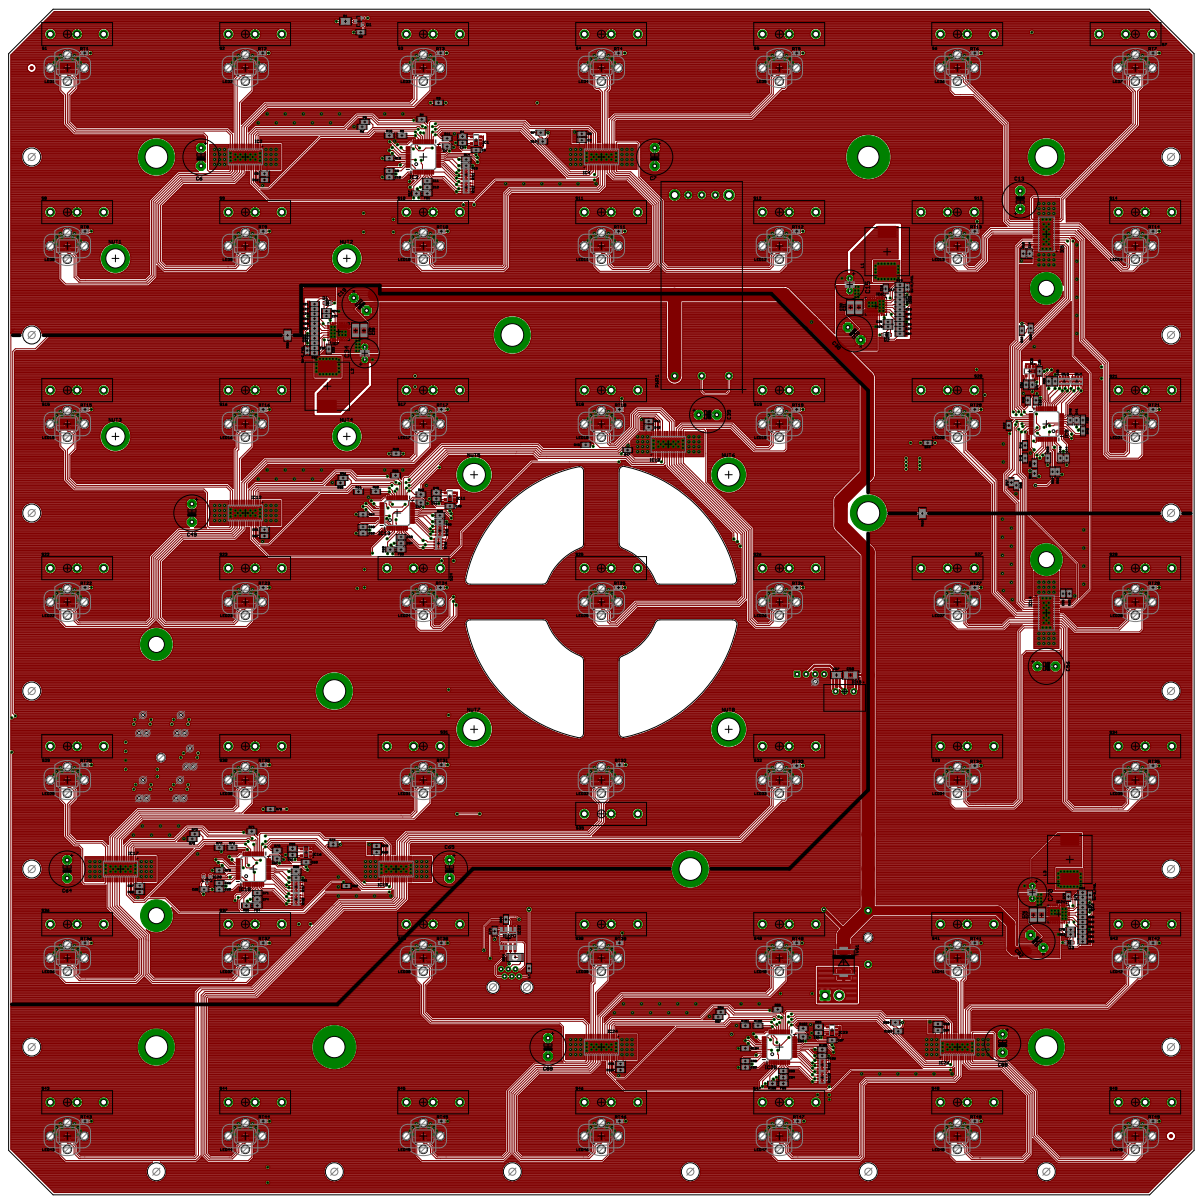
[picture p56: page 1]
